Modelyze/morap/end-effectors/pen/cad/README.md

# CAD for the Pen End Effector

Contains files in .stl format for the pen end effector and an Arduino board holder designed to fit on a 20x20 mm aluminum profiles used for this project. Also contains source files.
