Modelyze/morap/end-effectors/pen/drivers/README.md

# C drivers for the Pen End Effector

Include this file when you want to use the pen end effector in your system
