Modelyze/morap/joints/dc-motor-joint/hardware/misc/README.md

Miscellaneous parts

[general_purpose](./general_purpose) contains cad-models for general things. That is one arduino holder designed around the aluminum links for attaching boards with the arduino form-factor. It also contains a 45 degree bracket for said aluminum links which utilizes the same screws as the normal 90 degree bracket.
