Modelyze/morap/end-effectors/pen/cad/Solid Edge Source/README.md

# CAD Source Files

Developed in Solid Edge ST8, academic version
