Modelyze/morap/joints/dc-motor-joint/hardware/32mm_joint/32mm Joint P3.stl

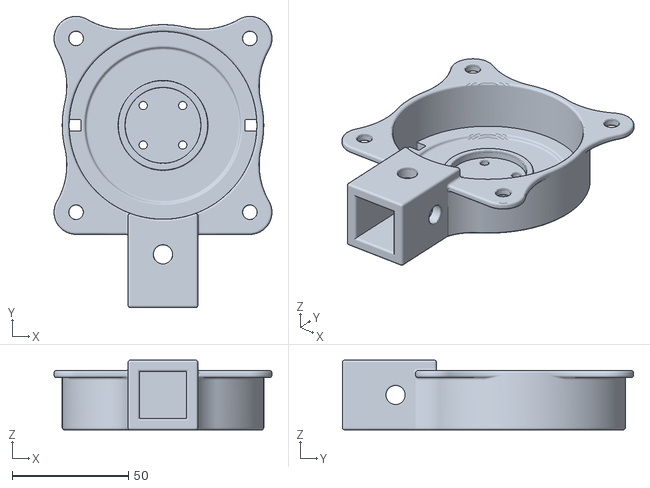
[picture p50: CAD file, 2016-02-08]
joints/dc-motor-joint/hardware/32mm_joint/32mm Joint P3.stl
93.7 x 125.1 x 30.0
