Modelyze/morap/joints/pendulum-joint/hardware/shaft-connect.stl

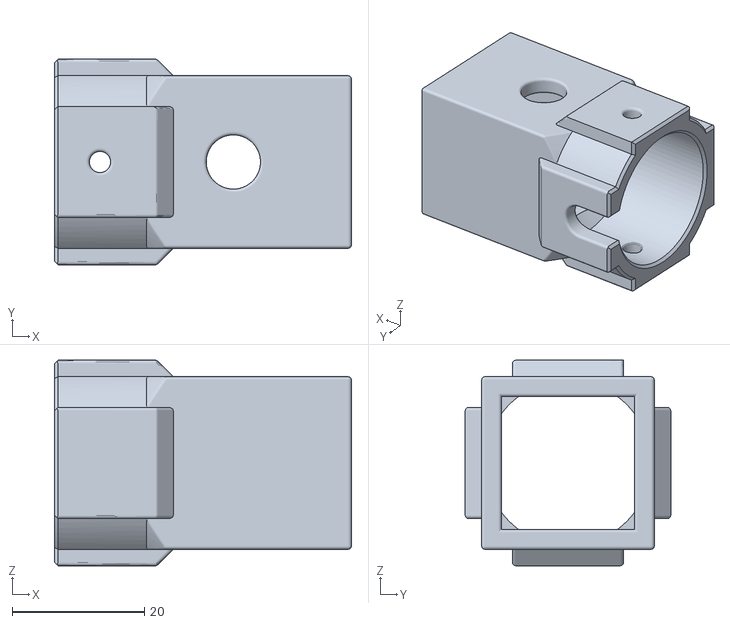
[picture p51: CAD file, 2016-03-08]
joints/pendulum-joint/hardware/shaft-connect.stl
45.0 x 31.1 x 31.1
