Modelyze/morap/joints/dc-motor-joint/hardware/22mm_joint/22mm Joint P3.stl

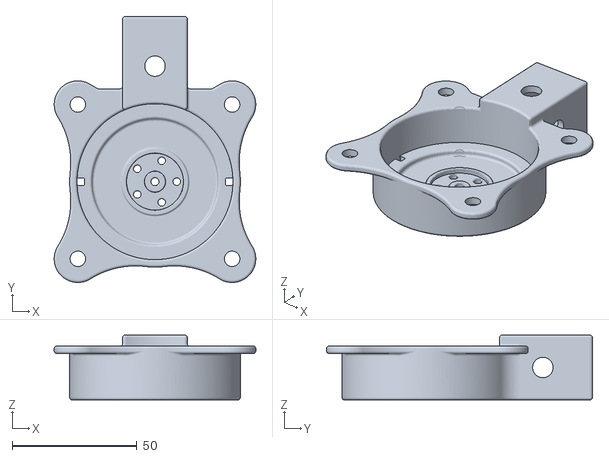
[picture p52: CAD file, 2016-02-08]
joints/dc-motor-joint/hardware/22mm_joint/22mm Joint P3.stl
80.9 x 106.7 x 26.0
