Modelyze/morap/joints/dc-motor-joint/hardware/32mm_joint/32mm Joint P1.stl

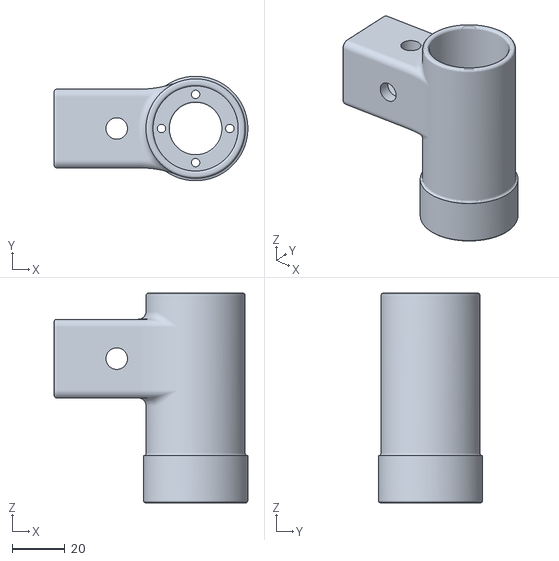
[picture p53: CAD file, 2016-02-08]
joints/dc-motor-joint/hardware/32mm_joint/32mm Joint P1.stl
73.8 x 39.8 x 80.0
