Modelyze/morap/joints/dc-motor-joint/hardware/22mm_joint/22mm Joint P2.stl

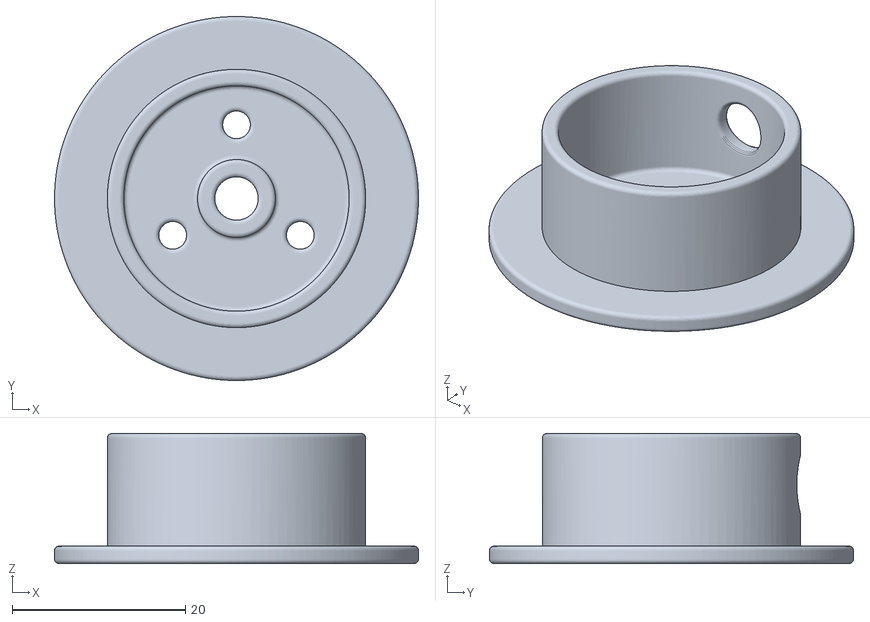
[picture p54: CAD file, 2016-02-08]
joints/dc-motor-joint/hardware/22mm_joint/22mm Joint P2.stl
42.0 x 42.0 x 15.0
