Modelyze/morap/joints/dc-motor-joint/hardware/22mm_joint/22mm PCB_holder.stl

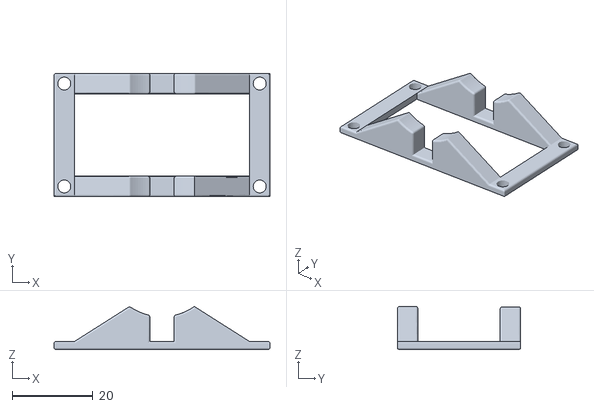
[picture p55: CAD file, 2016-02-08]
joints/dc-motor-joint/hardware/22mm_joint/22mm PCB_holder.stl
53.3 x 30.5 x 10.6
