Modelyze/morap/joints/dc-motor-joint/hardware/32mm_joint/8mm_shaft_attach.stl

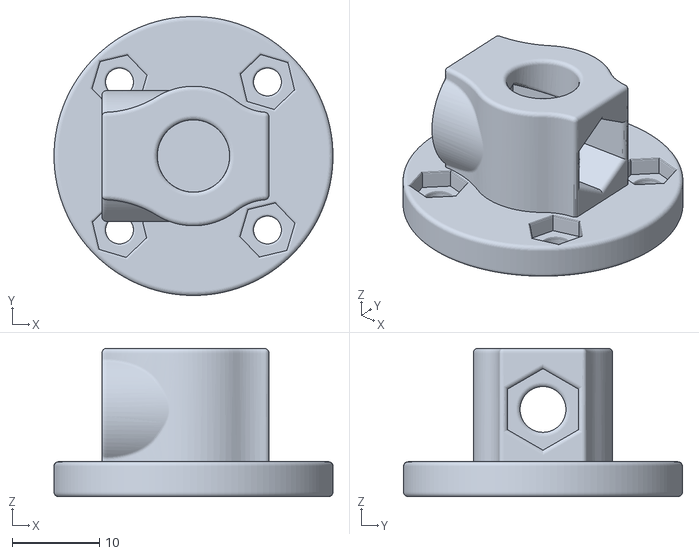
[picture p56: CAD file, 2016-02-08]
joints/dc-motor-joint/hardware/32mm_joint/8mm_shaft_attach.stl
32.0 x 32.0 x 17.0
