Modelyze/morap/joints/dc-motor-joint/hardware/22mm_joint/22mm Joint P4.stl

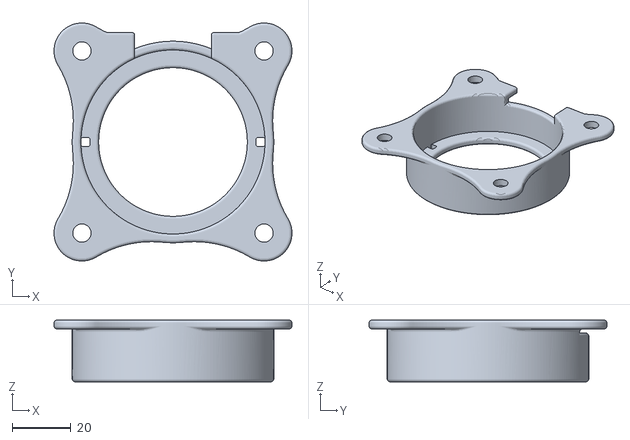
[picture p57: CAD file, 2016-02-08]
joints/dc-motor-joint/hardware/22mm_joint/22mm Joint P4.stl
80.9 x 80.9 x 21.0
