Modelyze/morap/joints/dc-motor-joint/hardware/32mm_joint/32mm Joint P2.stl

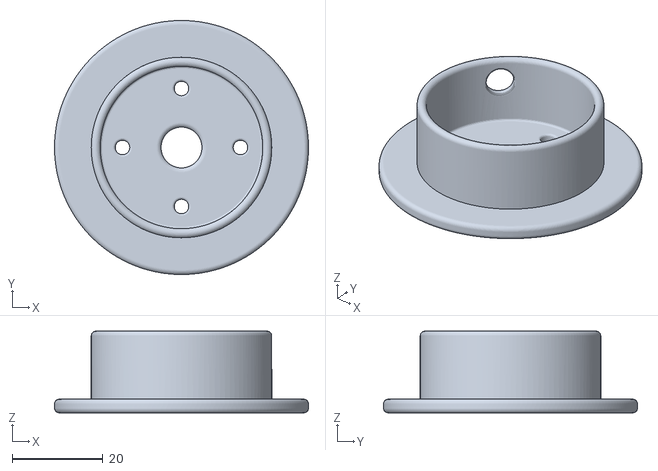
[picture p58: CAD file, 2016-02-08]
joints/dc-motor-joint/hardware/32mm_joint/32mm Joint P2.stl
56.0 x 56.0 x 18.0
